Ardrake/RasPiBot/Documentation/AdafruitServoHat/raspberry_pi_Schem1.png

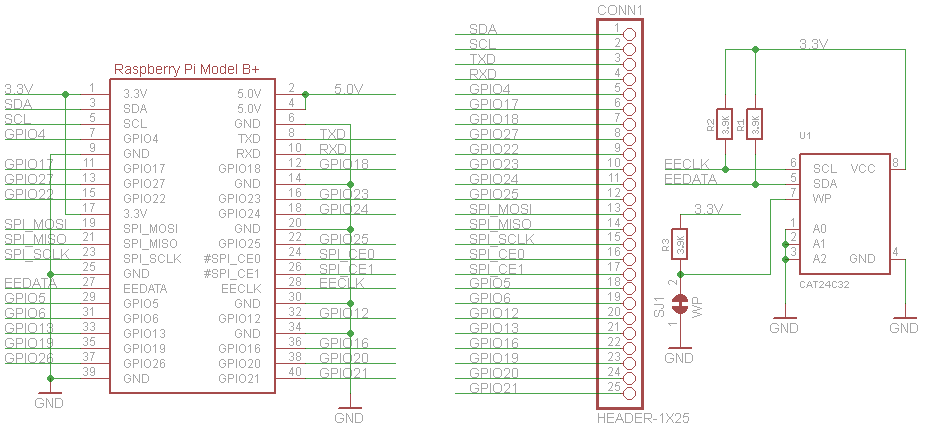
Documentation/AdafruitServoHat/raspberry_pi_Schem1.png
