Ardrake/RasPiBot/Images/backplate.jpg

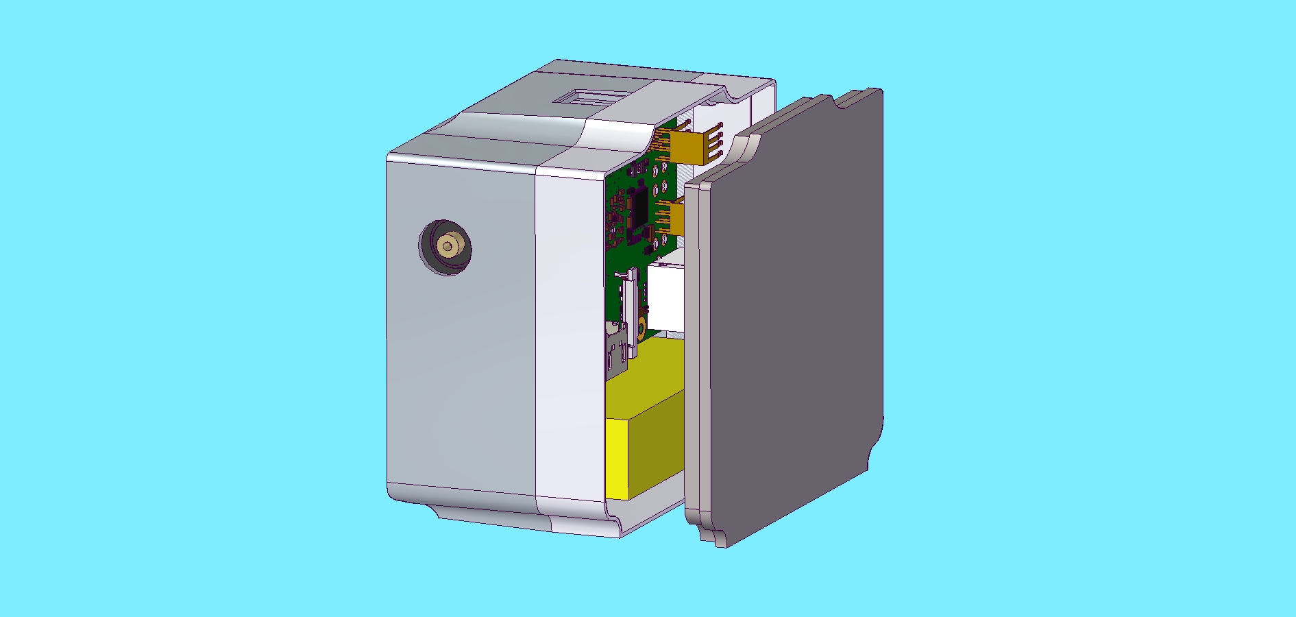
Images/backplate.jpg
