Ardrake/RasPiBot/Images/P4_A-01-01_Cooke.jpg

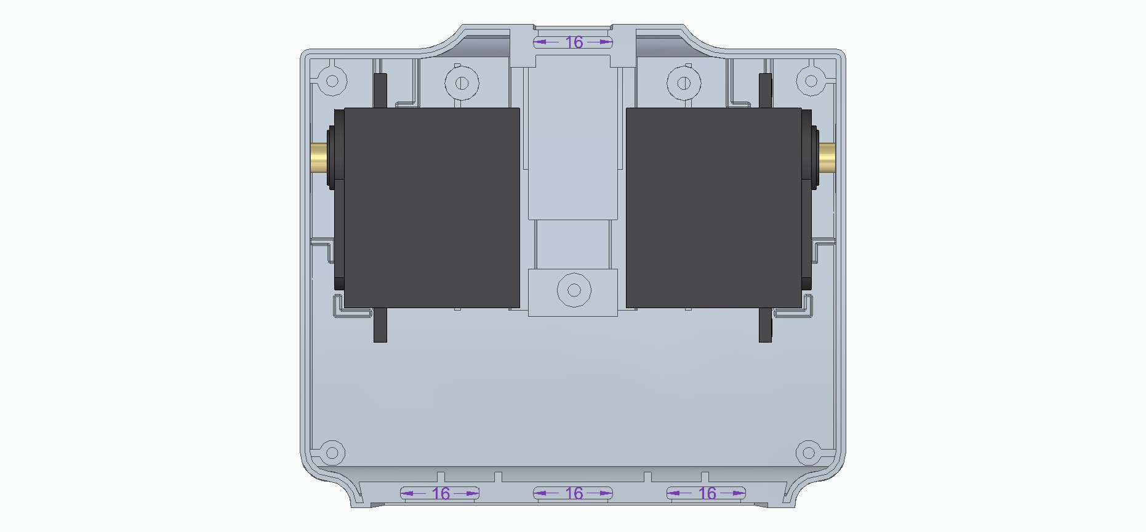
Images/P4_A-01-01_Cooke.jpg
