Ardrake/RasPiBot/Images/P4_A-01-02_Cooke.jpg

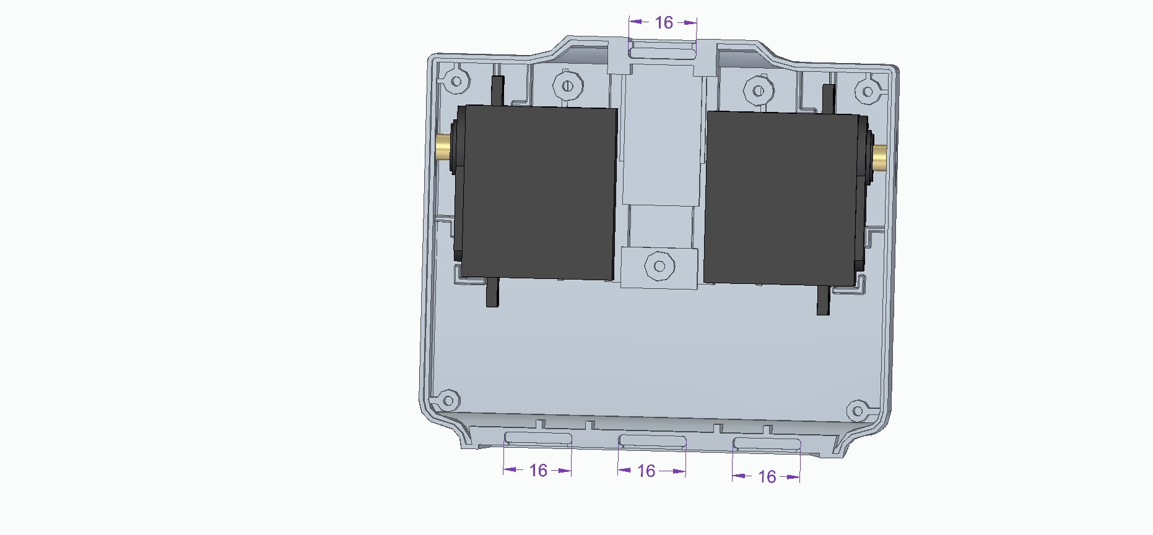
Images/P4_A-01-02_Cooke.jpg
