Ardrake/RasPiBot/Images/P7_A-01_Cooke.jpg

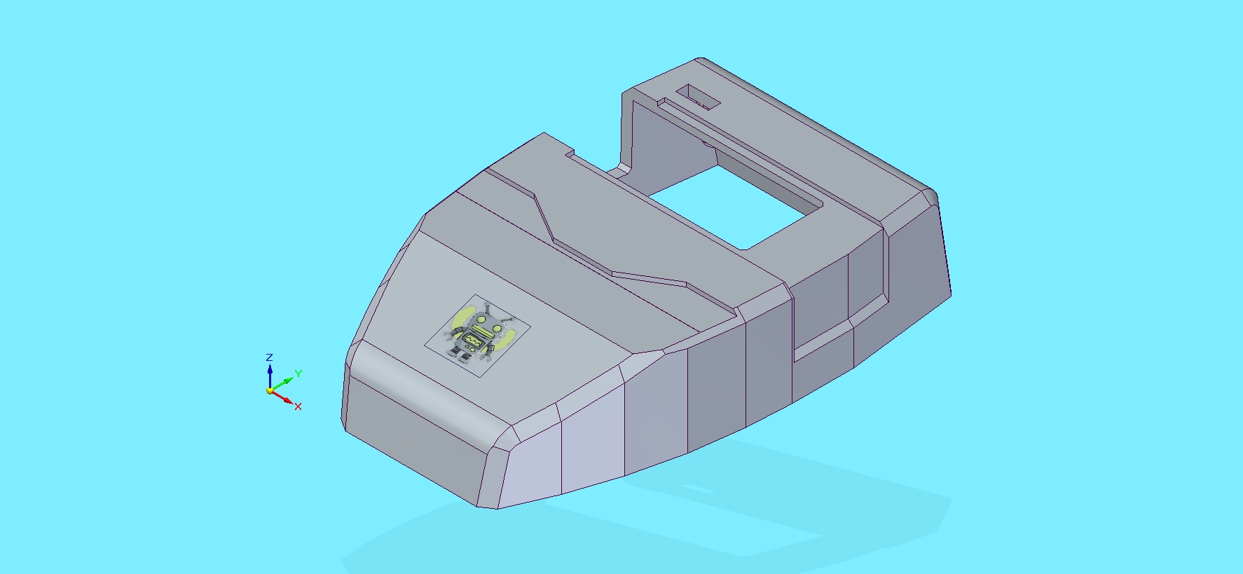
Images/P7_A-01_Cooke.jpg
