Ardrake/RasPiBot/Images/P21_A-01_Cooke.jpg

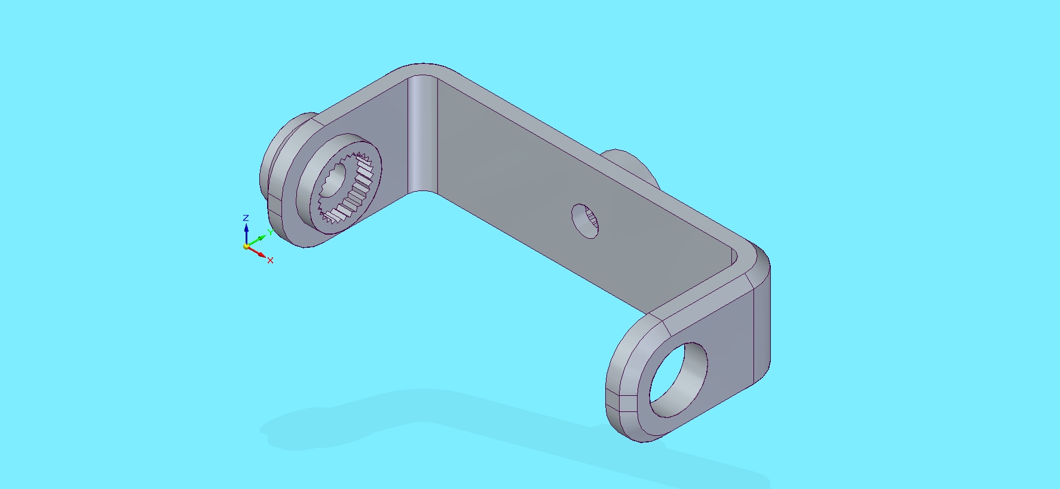
Images/P21_A-01_Cooke.jpg
