Ardrake/RasPiBot/Images/P23_A-01_MG996R.jpg

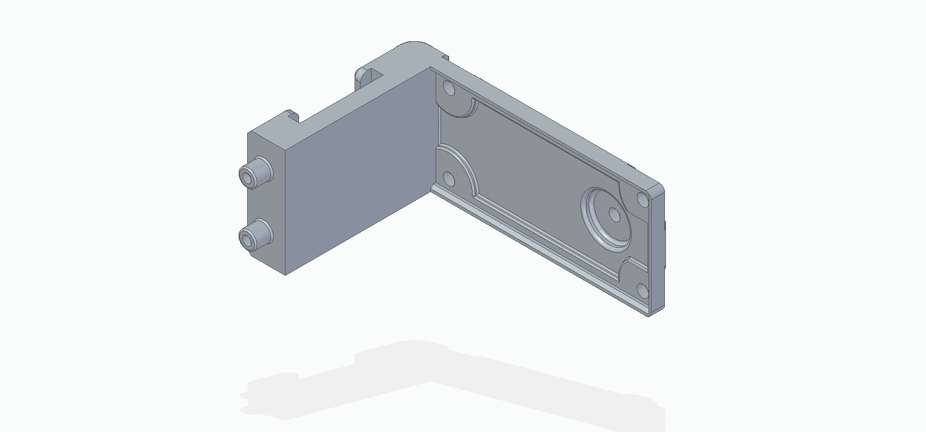
Images/P23_A-01_MG996R.jpg
