Ardrake/RasPiBot/Images/P24_A-01_MG996R.jpg

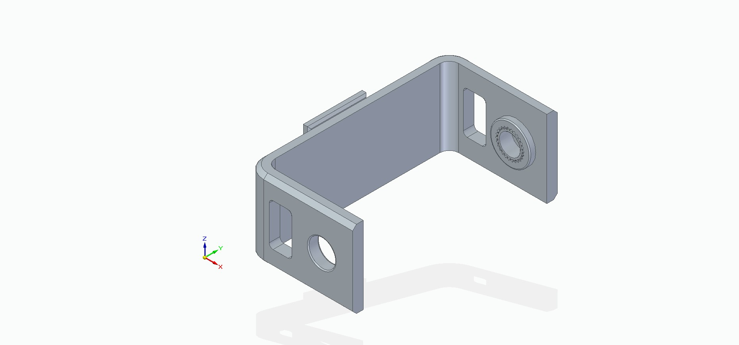
Images/P24_A-01_MG996R.jpg
