Ardrake/RasPiBot/Images/RasPiBot.jpg

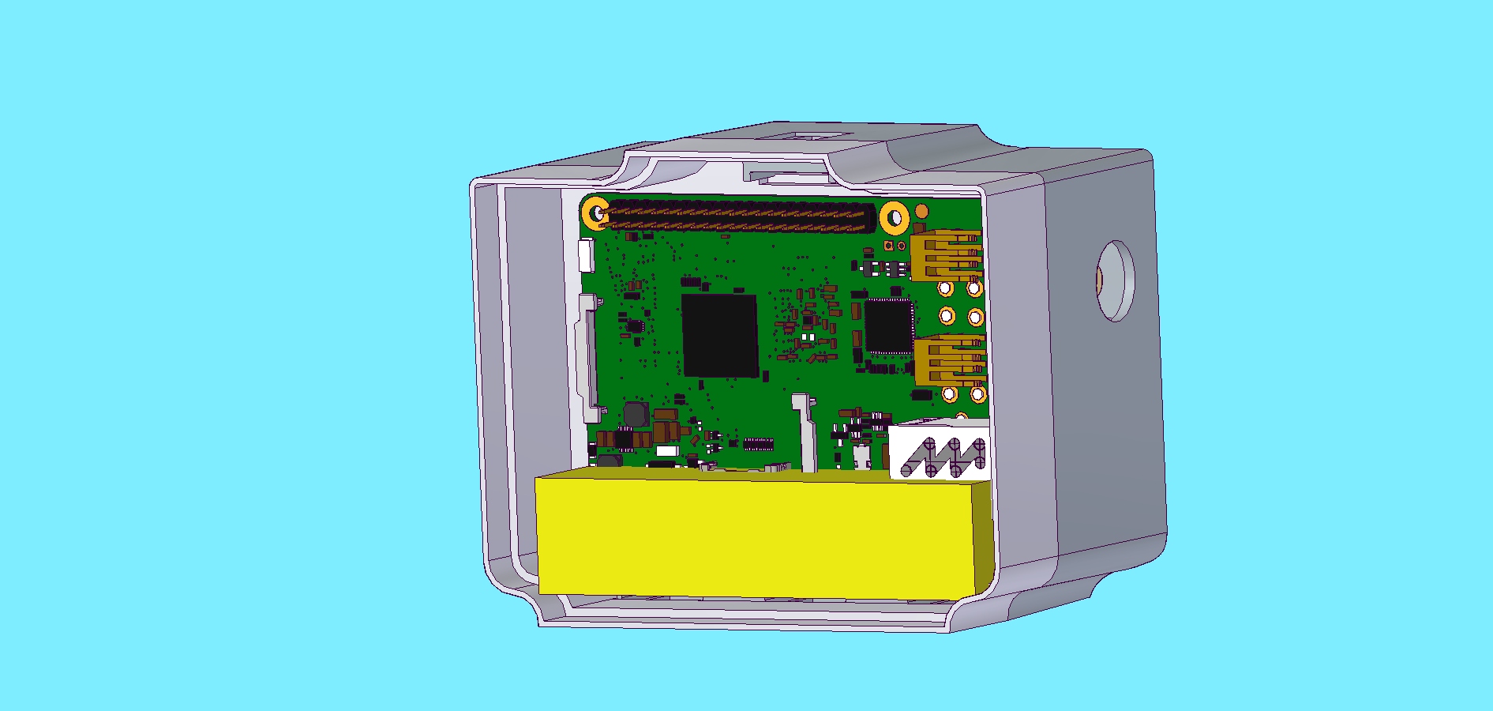
Images/RasPiBot.jpg
