Ardrake/RasPiBot/Images/RasPiBot_01.jpg

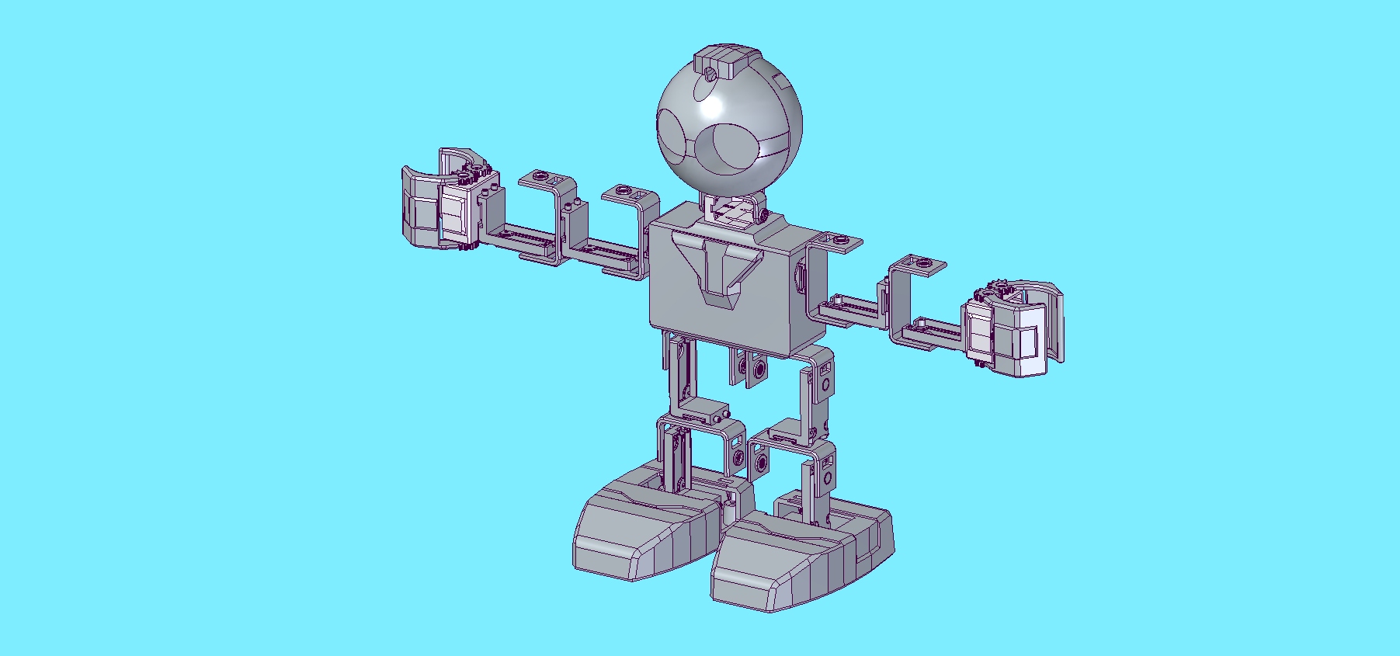
Images/RasPiBot_01.jpg
