Ardrake/RasPiBot/Images/RasPiBot_02.jpg

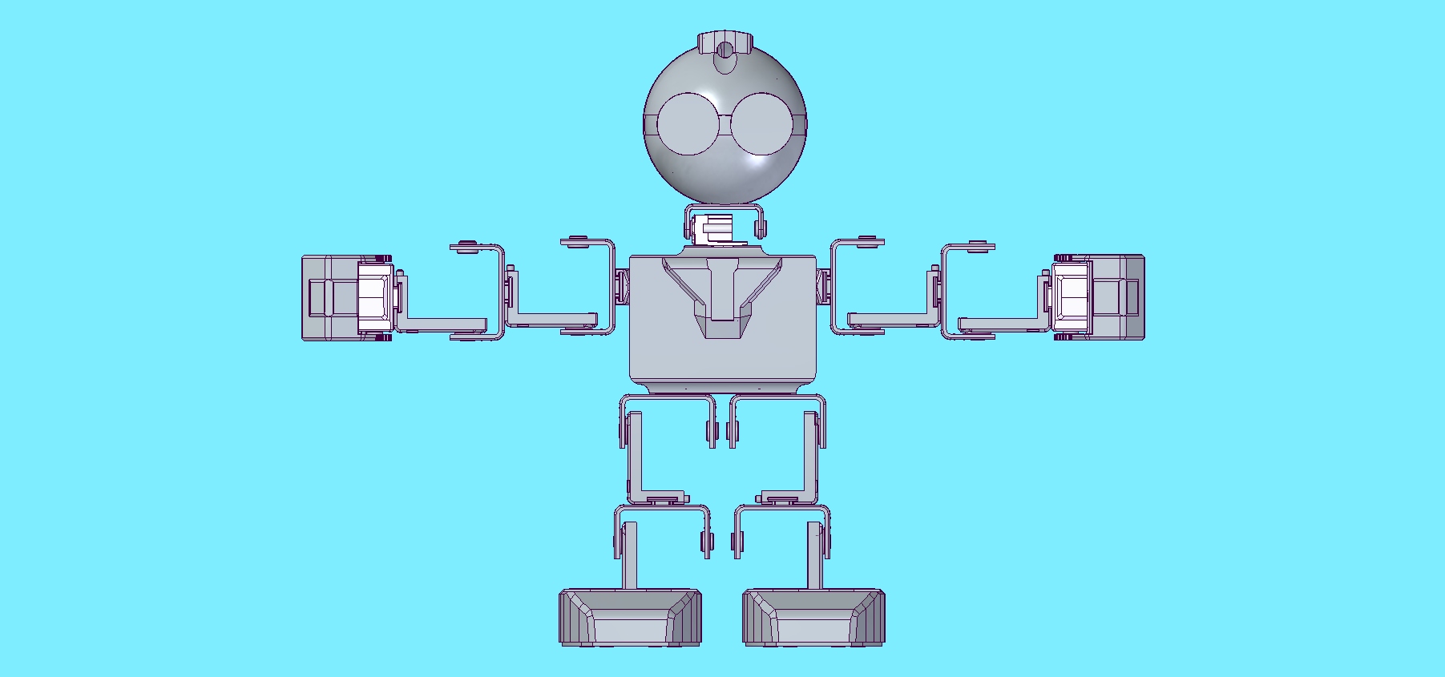
Images/RasPiBot_02.jpg
