Ardrake/RasPiBot/Images/RasPiBot_03.jpg

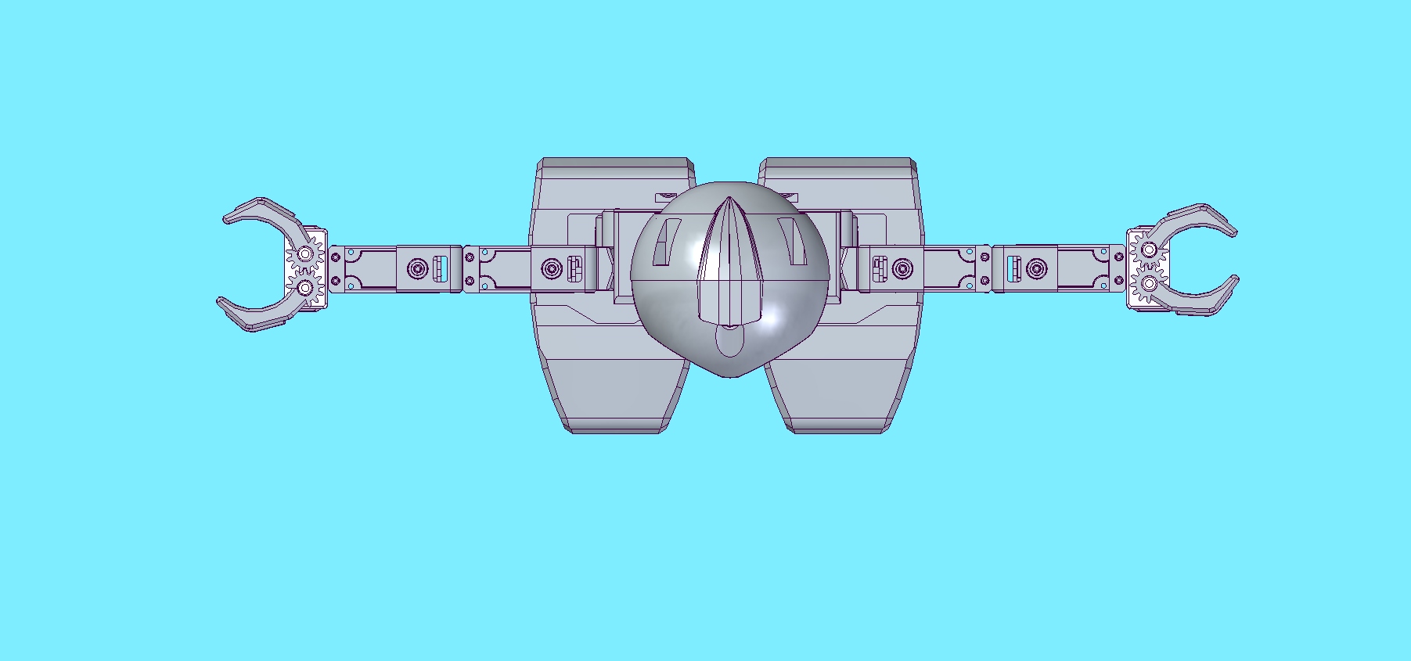
Images/RasPiBot_03.jpg
