Ardrake/RasPiBot/Images/VueServo01.jpg

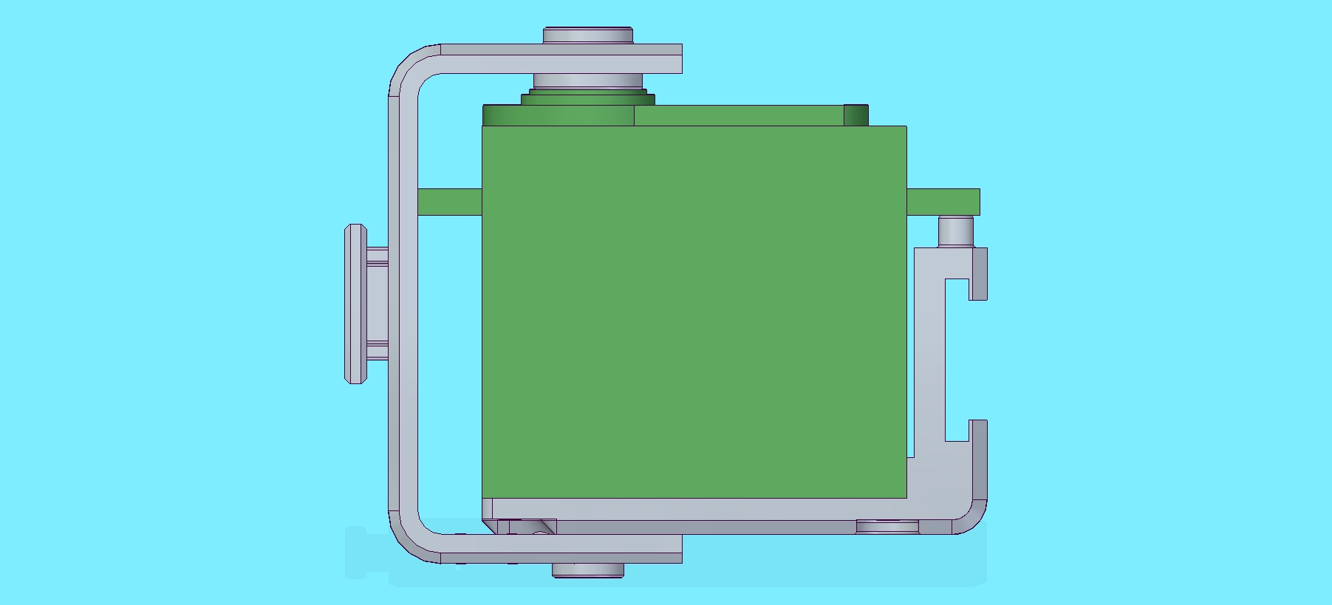
Images/VueServo01.jpg
