Ardrake/RasPiBot/Images/VueServo02.jpg

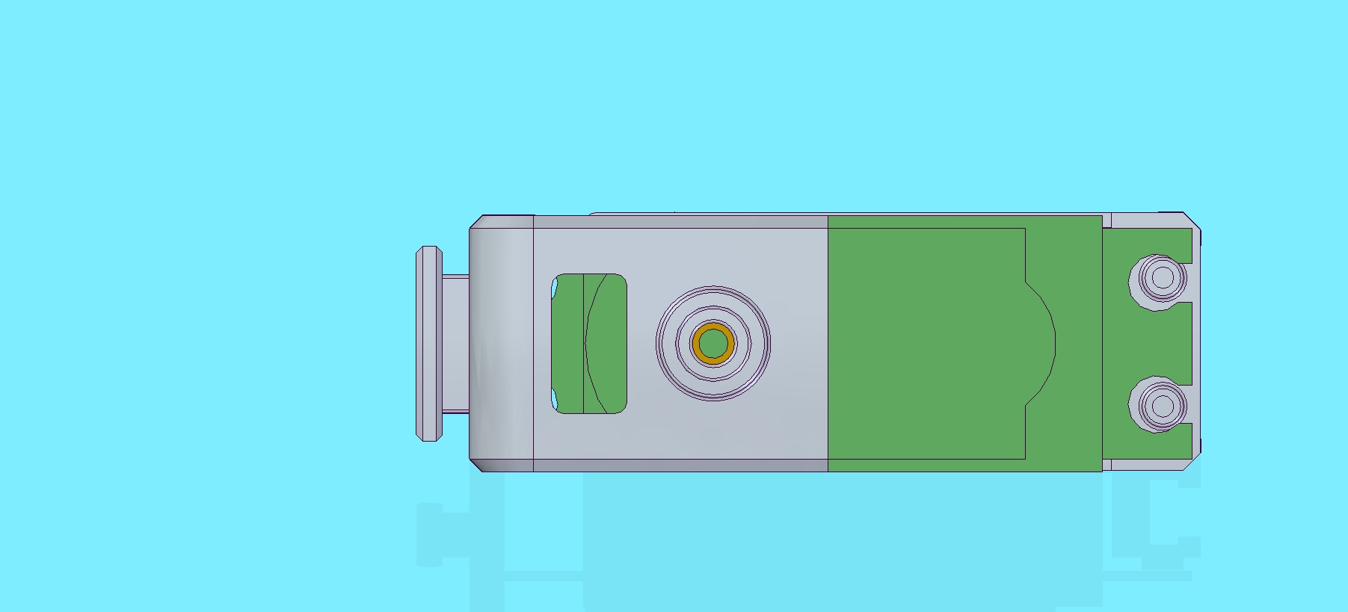
Images/VueServo02.jpg
