Ardrake/RasPiBot/stl/P11_A-01_Cooke.stl

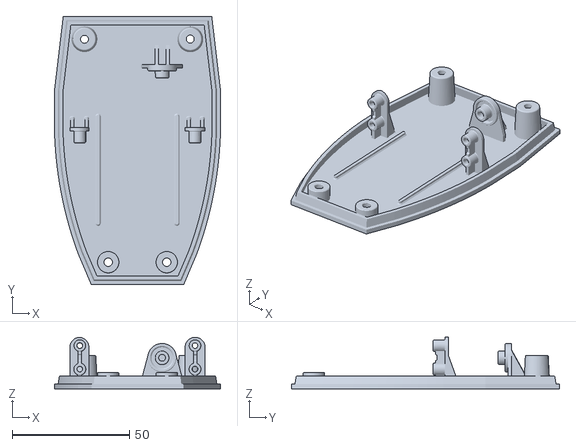
[picture p32: CAD file, 2017-07-11]
stl/P11_A-01_Cooke.stl
70.7 x 114.2 x 21.9
