Ardrake/RasPiBot/stl/P7_A-01_Cooke.stl

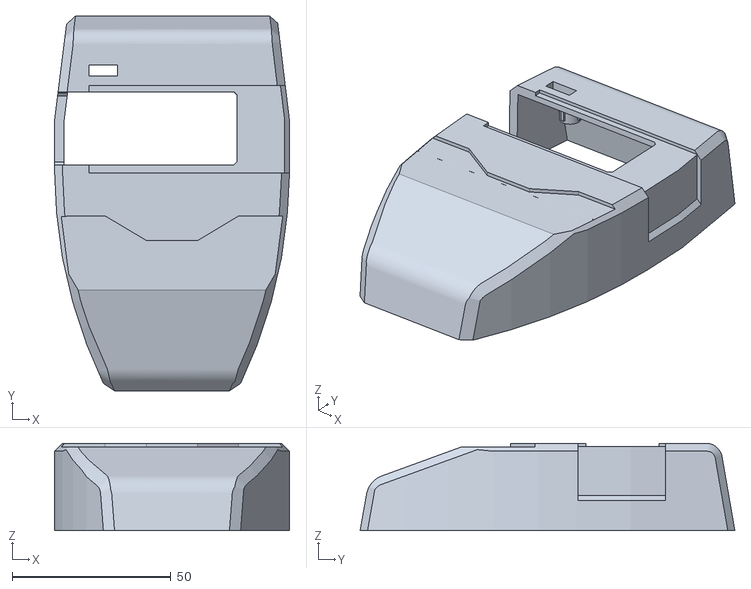
[picture p33: CAD file, 2017-07-11]
stl/P7_A-01_Cooke.stl
73.9 x 117.9 x 27.5
