Ardrake/RasPiBot/stl/P24_A-01_MG996R.stl

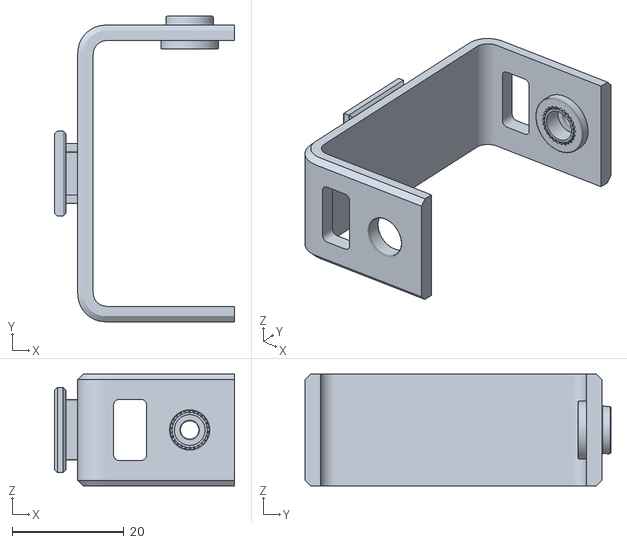
[picture p34: CAD file, 2017-07-06]
stl/P24_A-01_MG996R.stl
32.2 x 54.6 x 20.0
