Ardrake/RasPiBot/stl/P21_A-01.STL

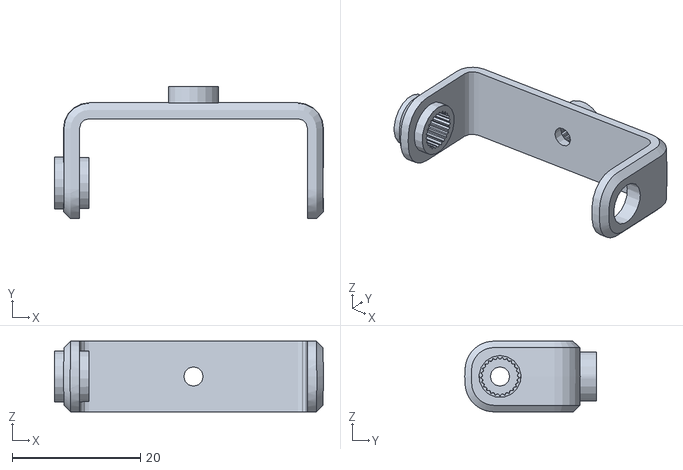
[picture p35: CAD file, 2017-07-04]
stl/P21_A-01.STL
41.9 x 20.5 x 11.0
