Ardrake/RasPiBot/stl/P43_A-01.STL

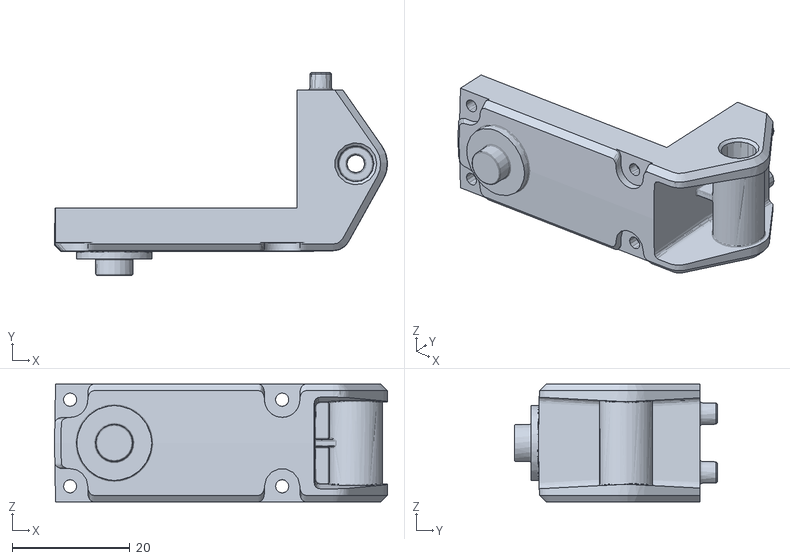
[picture p36: CAD file, 2017-07-04]
stl/P43_A-01.STL
56.5 x 34.5 x 20.0
