Ardrake/RasPiBot/stl/P2_A-01.STL

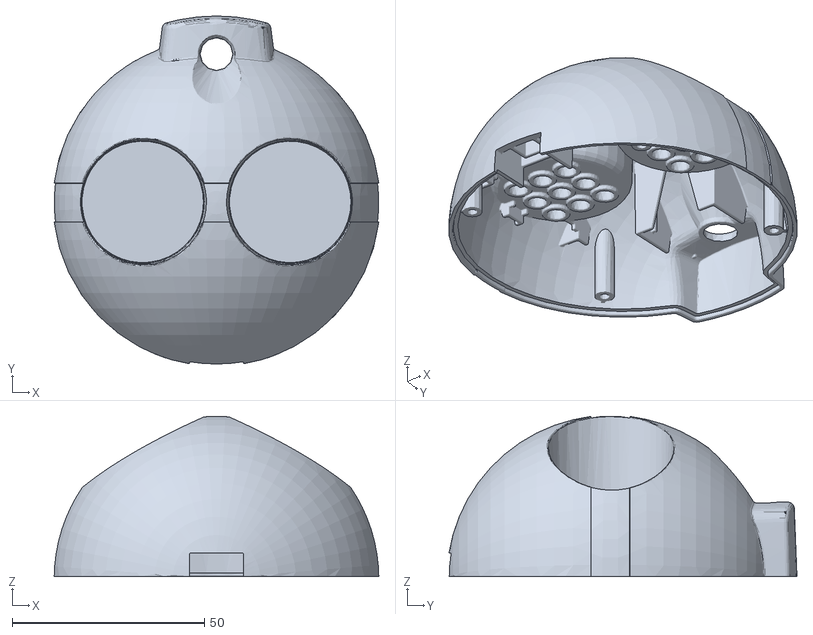
[picture p37: CAD file, 2017-07-04]
stl/P2_A-01.STL
84.4 x 90.4 x 41.7
