Ardrake/RasPiBot/stl/P5_A-01.STL

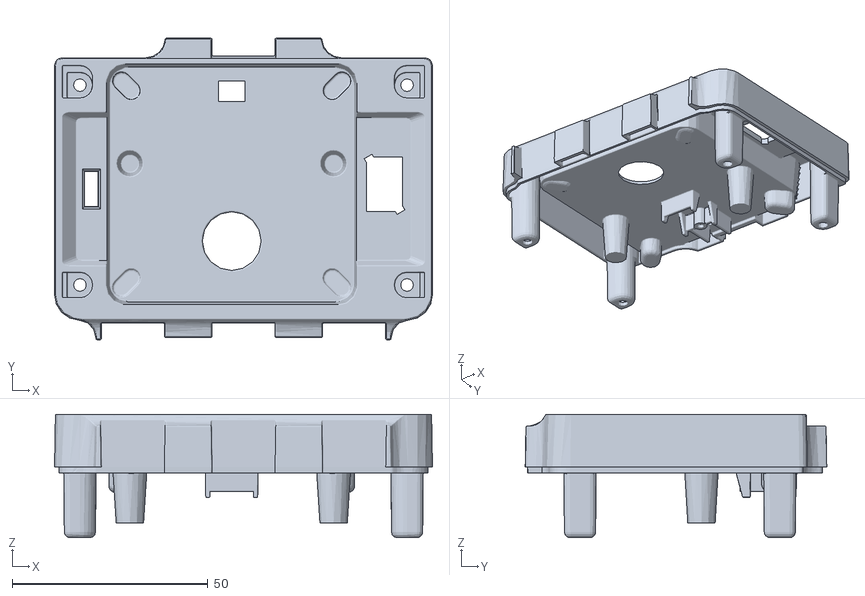
[picture p38: CAD file, 2017-07-04]
stl/P5_A-01.STL
96.5 x 77.0 x 31.5
