Ardrake/RasPiBot/stl/P20_A-01.STL

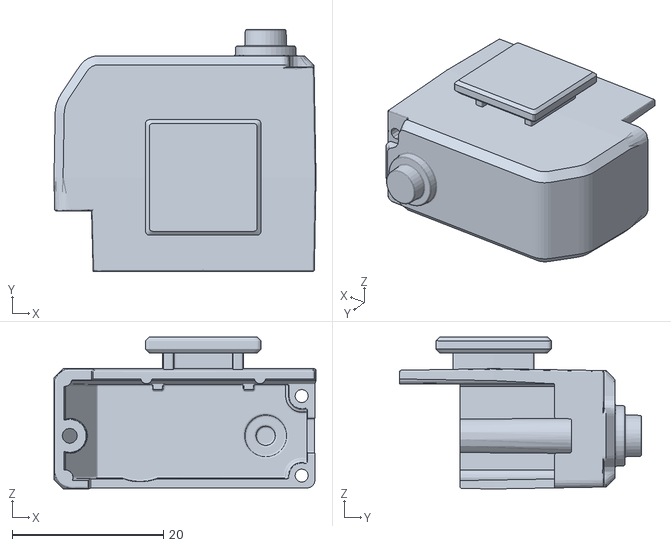
[picture p39: CAD file, 2017-07-04]
stl/P20_A-01.STL
34.6 x 32.0 x 20.1
