Ardrake/RasPiBot/stl/P3_A-01.STL

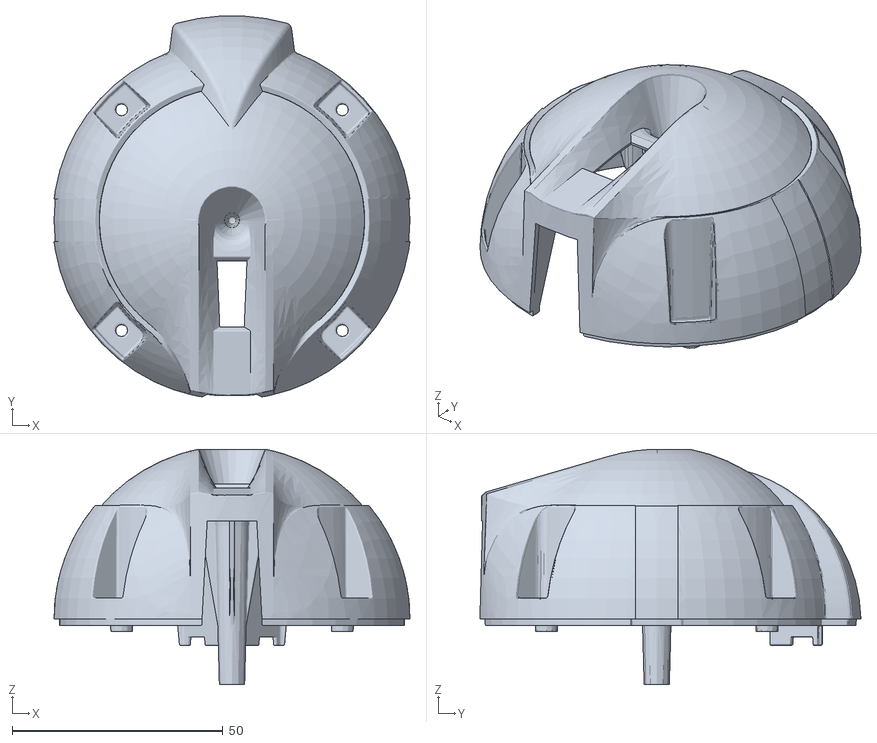
[picture p40: CAD file, 2017-07-04]
stl/P3_A-01.STL
84.4 x 90.3 x 55.7
