Ardrake/RasPiBot/test/Model MG996R/V3/IMG_0258.JPG

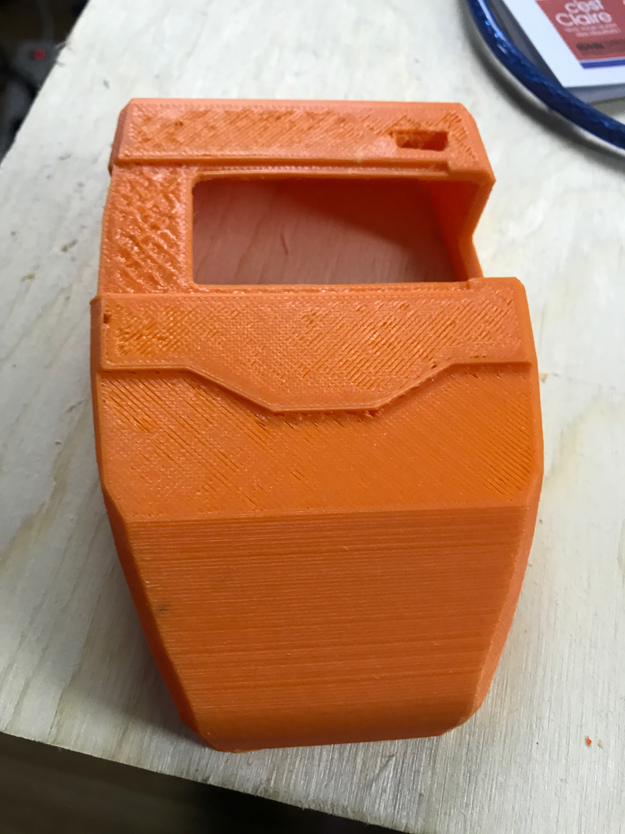
test/Model MG996R/V3/IMG_0258.JPG
