Ardrake/RasPiBot/test/Model MG996R/V3/IMG_0294.jpg

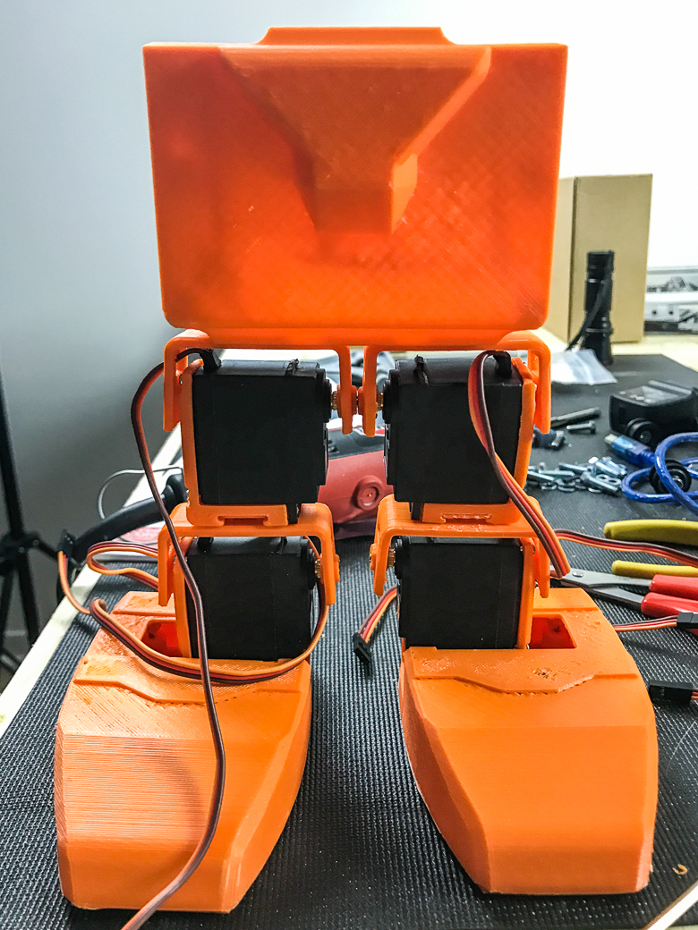
test/Model MG996R/V3/IMG_0294.jpg
