Ardrake/RasPiBot/test/Model MG996R/V3/IMG_0296.JPG

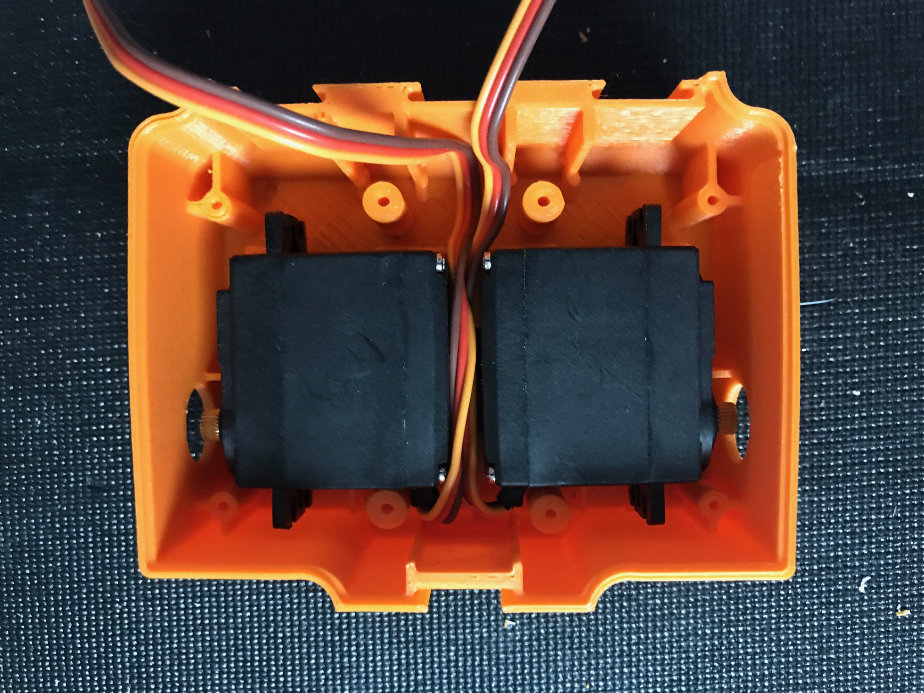
test/Model MG996R/V3/IMG_0296.JPG
