Ardrake/RasPiBot/test/Model MG996R/V3/IMG_0308.JPG

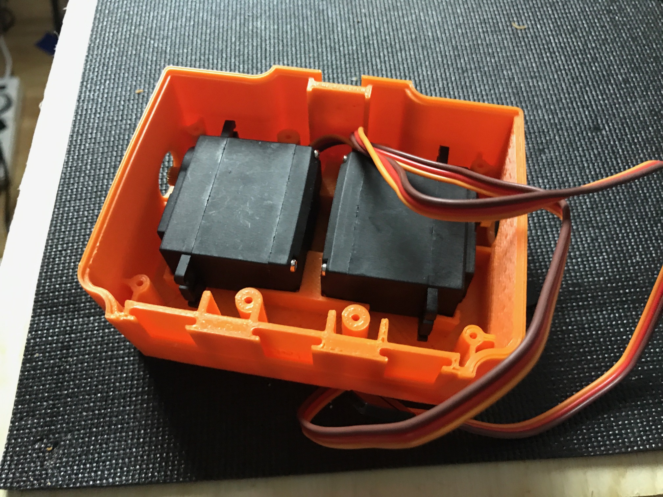
test/Model MG996R/V3/IMG_0308.JPG
