Ardrake/RasPiBot/test/Model MG996R/V3/IMG_0311.jpg

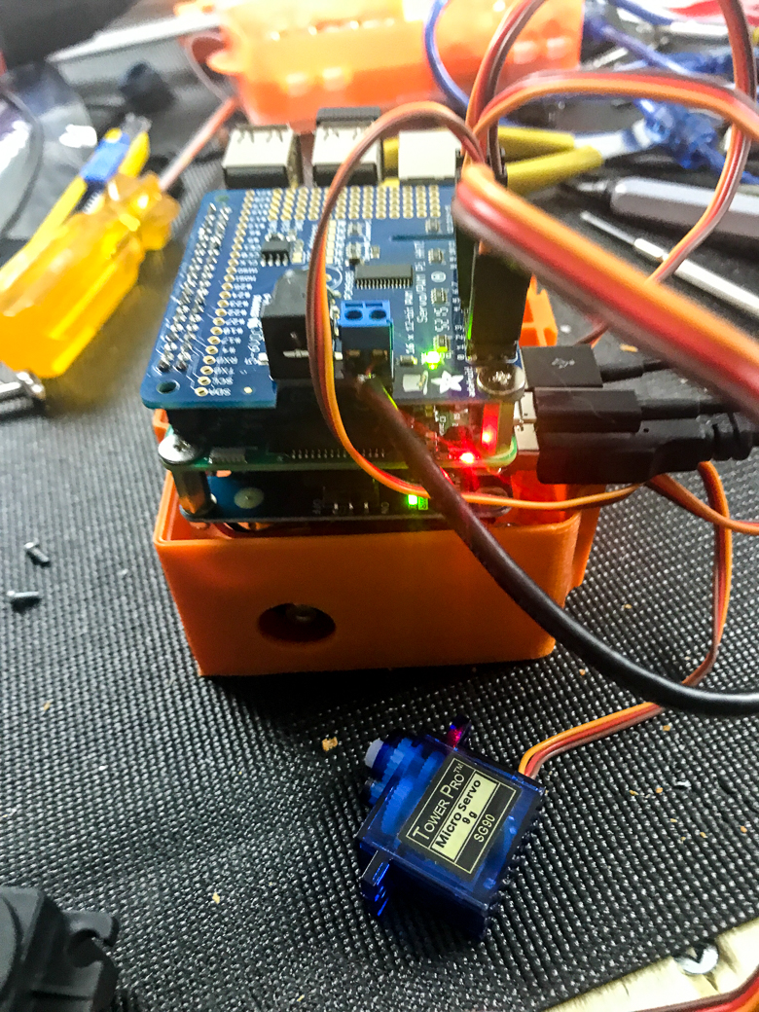
test/Model MG996R/V3/IMG_0311.jpg
