Ardrake/RasPiBot/test/Model MG996R/V3/IMG_0312.jpg

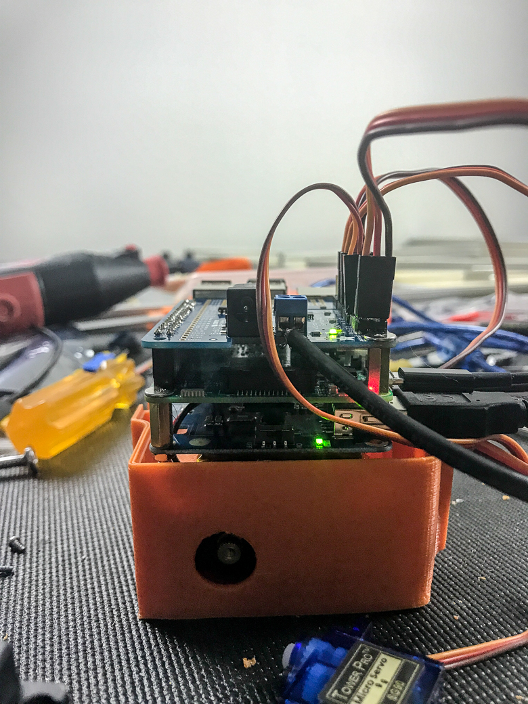
test/Model MG996R/V3/IMG_0312.jpg
