Ardrake/RasPiBot/test/Model MG996R/V3/IMG_0333.jpg

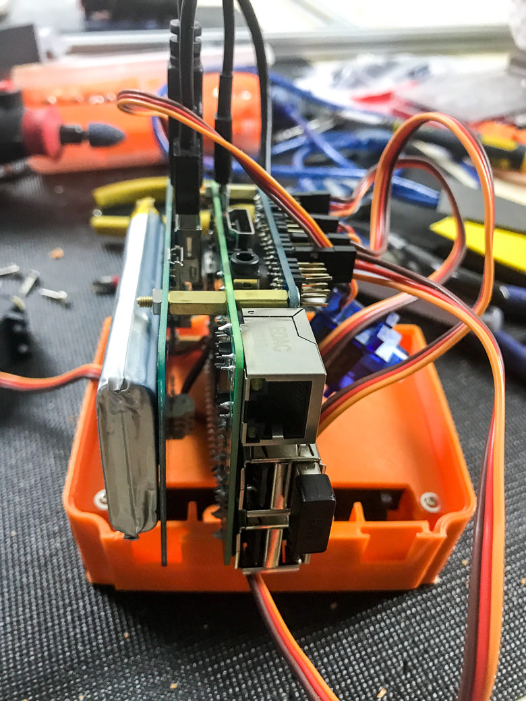
test/Model MG996R/V3/IMG_0333.jpg
